team4015/RGB-Controller/firmware/init.c

#include "init.h"

#include <xc.h>
#include <pic16f690.h>

#include "pins.h"

#define LED_DELAY     150000

void init_hardware(void)
{
	// ANALOGUE (1) / DIGITAL (0) //

	ANSEL  = 0b00000000;   // AN7, AN6, AN5, AN4, AN3,  AN2,  AN1, AN0
	ANSELH = 0b00000000;   // N/C, N/C, N/C, N/C, AN11, AN10, AN9, AN8

	// INPUT (1) / OUTPUT (0) //

	TRISA = 0b00000000;    // N/C, N/C, RA5, RA4, RA3,  RA2,  RA1, RA0
	TRISB = 0b00000000;    // RB7, RB6, RB5, RB4, N/C,  N/C,  N/C, N/C
	TRISC = 0b00000000;    // RC7, RC6, RC5, RC4, RC3,  RC2,  RC1, RC0

	// INITIALIZE IO REGISTERS //

	PORTA = 0b00000000;
	PORTB = 0b00000000;
	PORTC = 0b00000000;

	// OSCILLATOR FREQUENCY //

	OSCCONbits.IRCF = 0b111;      // Fosc = 8 MHz
	OSCCONbits.SCS = 1;           // use internal oscillator as system clock
	OSCTUNEbits.TUN = 0b00000;    // tune internal oscillator to factory-calibrated frequency

	init_indicator();       // flash status LEDs
}

void init_indicator(void)
{
	for (int i = 0; i < 3; i++)
	{
		LED = 1;
		_delay(LED_DELAY);
		LED = 0;
		_delay(LED_DELAY);
	}
}
